saoto28/pineapple60/p60-01/pcb.jpg

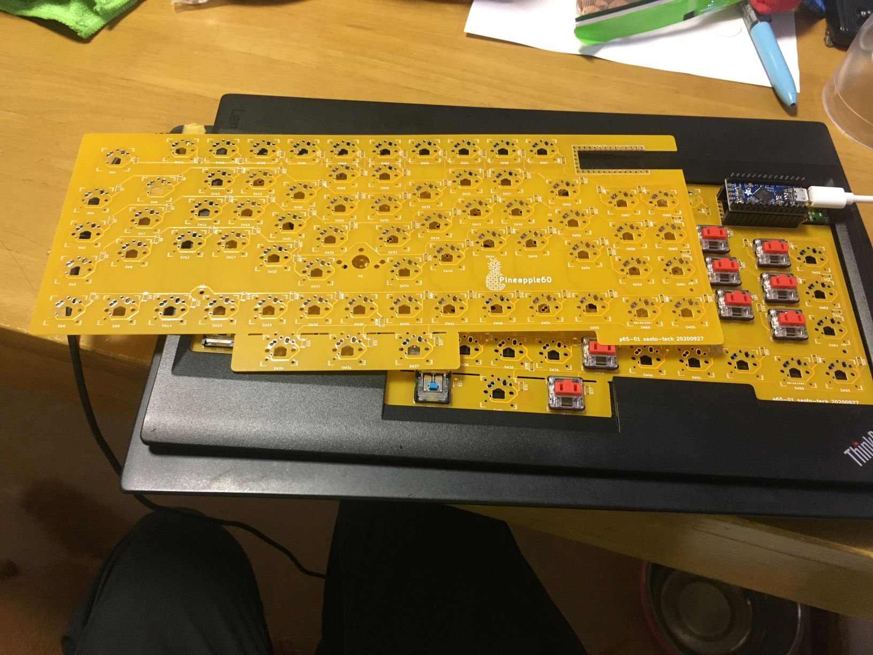
p60-01/pcb.jpg
