saoto28/pineapple60/p60S/p60s.jpg

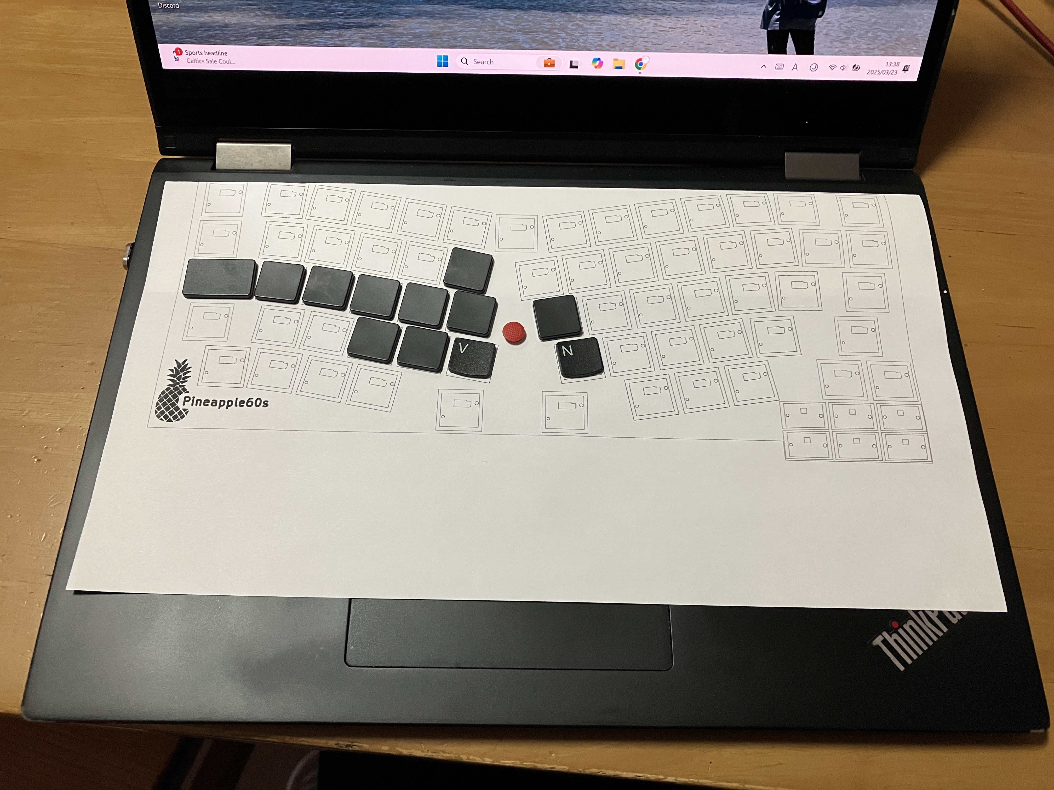
p60S/p60s.jpg
