saoto28/pineapple60/p60S/x13g2_v10.png

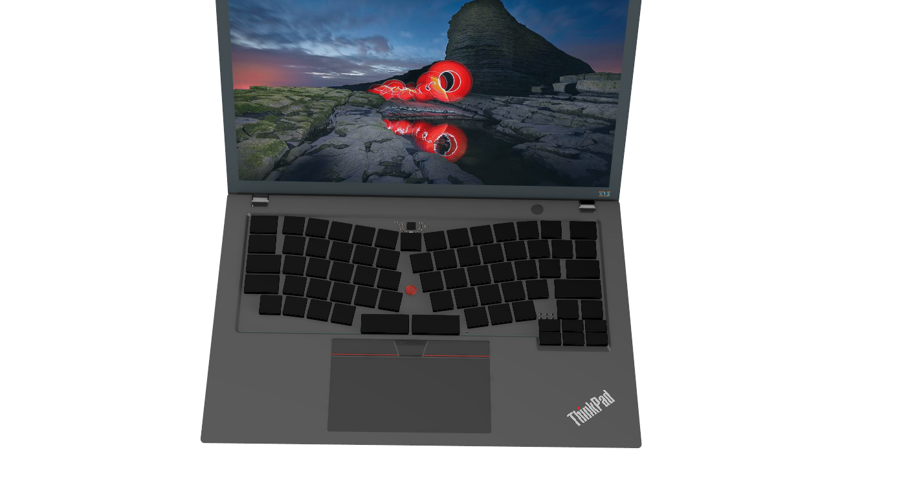
p60S/x13g2_v10.png
