saoto28/pineapple60/pics/00_cut_pcb0b.jpg

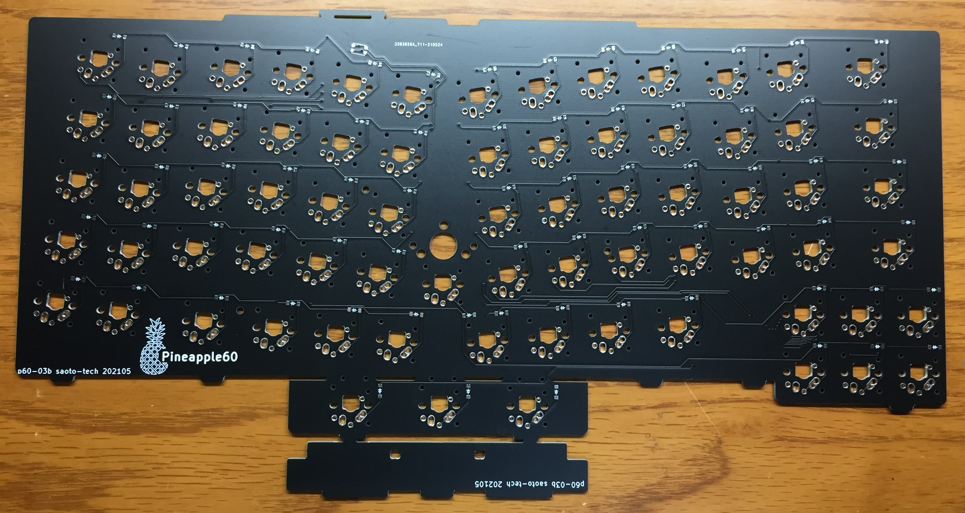
pics/00_cut_pcb0b.jpg
