saoto28/pineapple60/pics/01_cut_pcb1.jpg

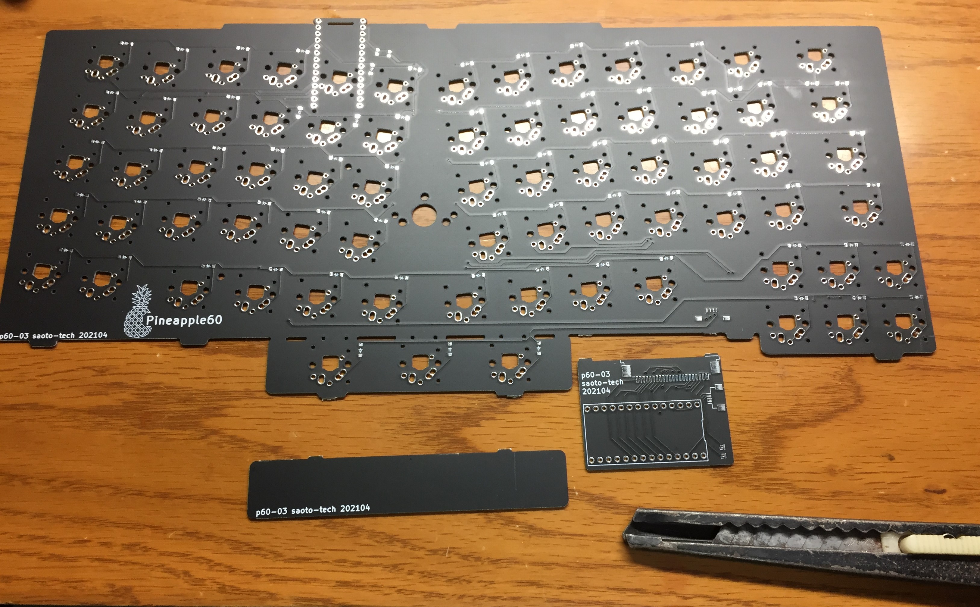
pics/01_cut_pcb1.jpg
