saoto28/pineapple60/pics/put_sw2.jpg

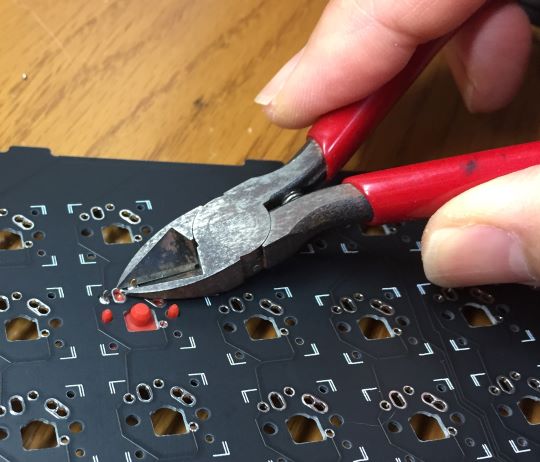
pics/put_sw2.jpg
