saoto28/pineapple60/p0/How_to_modify_MS_ergonomic_keyboard.files/image047.jpg

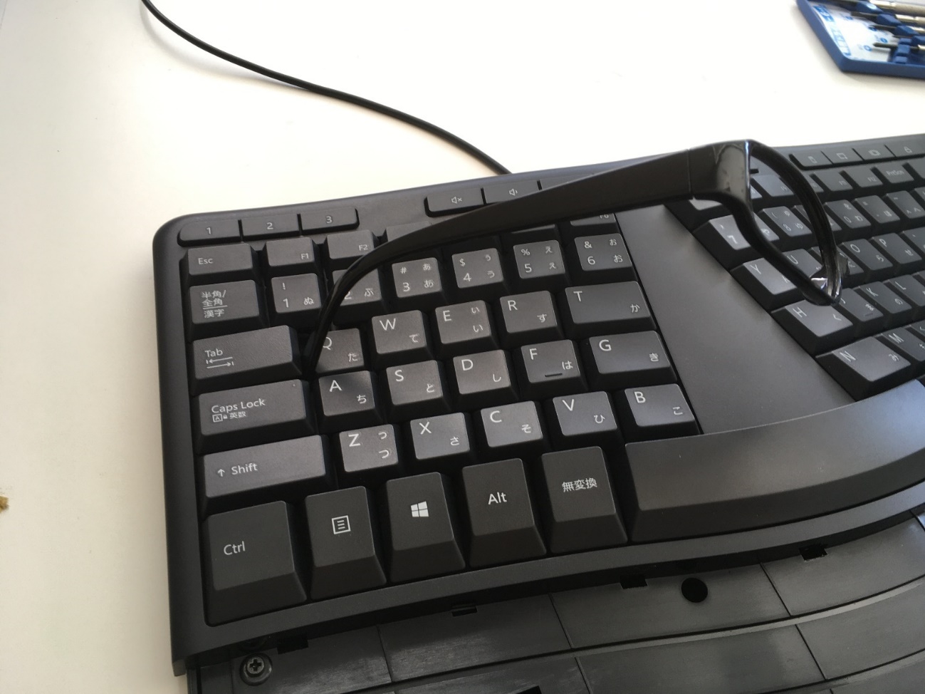
p0/How_to_modify_MS_ergonomic_keyboard.files/image047.jpg
