saoto28/pineapple60/pics/assemble_keyboard02.jpg

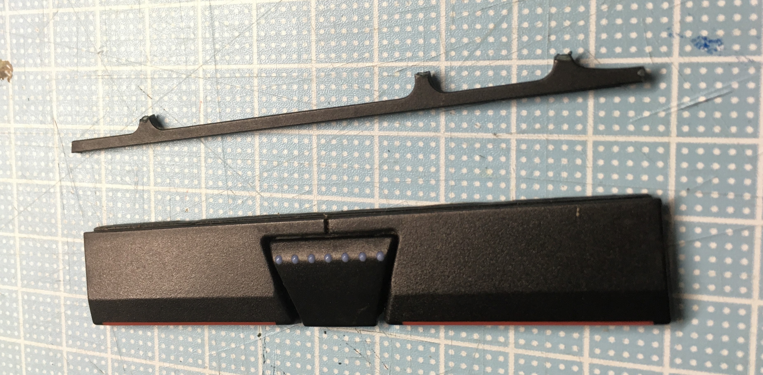
pics/assemble_keyboard02.jpg
