saoto28/pineapple60/pics/assemble_keyboard03.jpg

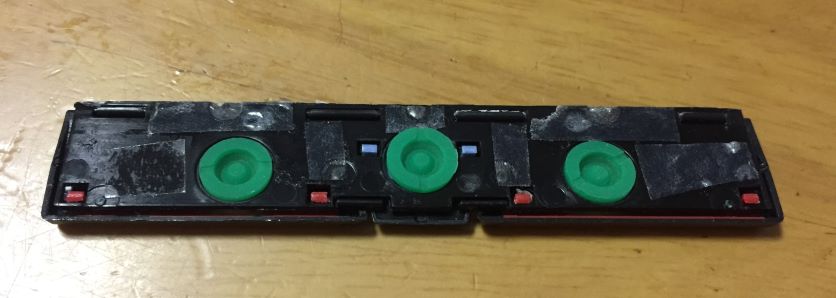
pics/assemble_keyboard03.jpg
