saoto28/pineapple60/pics/assemble_keyboard05.jpg

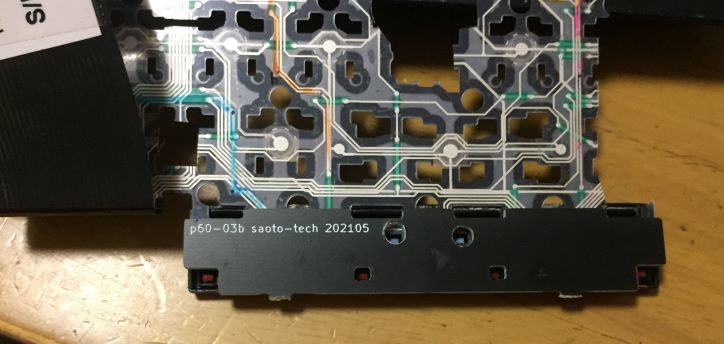
pics/assemble_keyboard05.jpg
