saoto28/pineapple60/pics/assemble_keyboard20.jpg

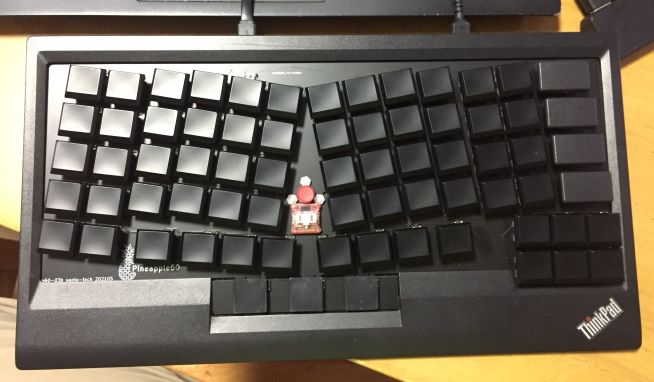
pics/assemble_keyboard20.jpg
