saoto28/pineapple60/pics/disassemble_keyboard14.jpg

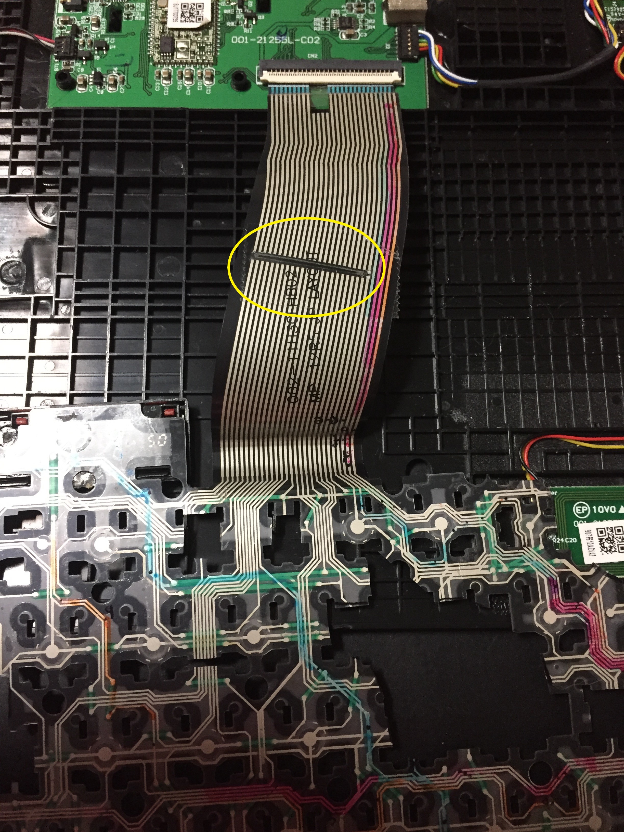
pics/disassemble_keyboard14.jpg
